ooggesen/Car/Code/Car_Backend/Bluetooth_functions.ino

#ifndef WIFI_N_BT

#include "my_bt.h"

int bluetooth_receiver(struct pt *pt){
  PT_BEGIN(pt);

  central = BLE.central();

  if (central) {
    Serial.print("Connected to central: ");
    Serial.println(central.address());

    while (central.connected()) {
      if (command.written()) {
//        println_debug(command.value());
        match_com((String) command.value());
      }
      PT_YIELD(pt);
    }

    // when the central disconnects, print it out:
    Serial.print(F("Disconnected from central: "));
    Serial.println(central.address());
  }
  
  PT_END(pt);
}

void init_bluetooth(){
  println_debug("Init Bluetooth!");
  if (!BLE.begin()) {
      Serial.println("Error in bluetooth init!");
      while (1);
    }

    BLE.setLocalName("car_control"); //name for advertisement
    BLE.setDeviceName("car_control"); //name of build in characteristic
    BLE.setAdvertisedService(car_control);
    car_control.addCharacteristic(command);
    car_control.addCharacteristic(photo_data);

    BLE.addService(car_control);

    command.writeValue("Init!");
    photo_data.writeValue(buff, sizeof(buff), true);

    println_debug("Start advertise!");
    if (!BLE.advertise()){
      println_debug("ERROR:");
      println_debug("Could not start advertising!");
    }
    print_debug("Started BT service with UUID: ");
    println_debug(car_control.uuid());
    println_debug("With characteristics: ");
    print_debug("Command: ");
    println_debug(command.uuid());
    print_debug("Photo_data: ");
    println_debug(photo_data.uuid());
    
    println_debug("Init done!");
}

void test_bt(){
  println_debug("Starting testing bluetooth!");
  String backup = command.value();
  char *test_string = "Test!";
  command.writeValue(test_string);
  String read_string = command.value();

  if (((String) test_string) != read_string){
    println_debug("ERROR:");
    println_debug("Could not write or read to command characteristic!"); 
    print_debug("Test string: ");
    print_debug(test_string);
    print_debug(" ,but read: ");
    println_debug(read_string);
    while(1);
  }else{
    command.writeValue(backup);
  }

  photo_data.writeValue(buff, sizeof(buff), true);
  const uint8_t* cmp_buff = photo_data.value();
  for (int i=0; i<sizeof(buff); i++){
    if (buff[i] != cmp_buff[i]){
      println_debug("ERROR:");
      println_debug("Could not write or read to charcteristic!");
    }
  }
  println_debug("Finished testing bluetooth!");
}

void send_data(char* data, size_t len){
  if (sizeof(data) == sizeof(buff)){
    photo_data.writeValue((void*) data, (int) sizeof(buff), true);
  } else {
    uint8_t new_buff[sizeof(buff)];
    for (int i=0; i<sizeof(buff); i++){
      if (i<(int) len){
        new_buff[i] = (uint8_t) *(data + i);
      } else {
        new_buff[i] = (uint8_t) 255;
      }
    }

    photo_data.writeValue((void*) new_buff, (int) sizeof(buff), true);
  }
}
#endif //WIFI_N_BT
