ooggesen/Car/Code/Car_Backend/arduino_secrets.h

 #ifndef ARDUINO_SECRETS.H
 #define ARDUINO_SECRETS.H
 
// #define SECRET_SSID "o2-WLAN37"
// #define SECRET_PASS "NQCR43332YQR4E8M"

#define SECRET_SSID "KatrinLan"
#define SECRET_PASS "PolliederCollie"

#endif //ARDUINO_SECRETS.H
